redhawk668/ZX-Spectrum-S-Video/IMG_20200522_165719.jpg

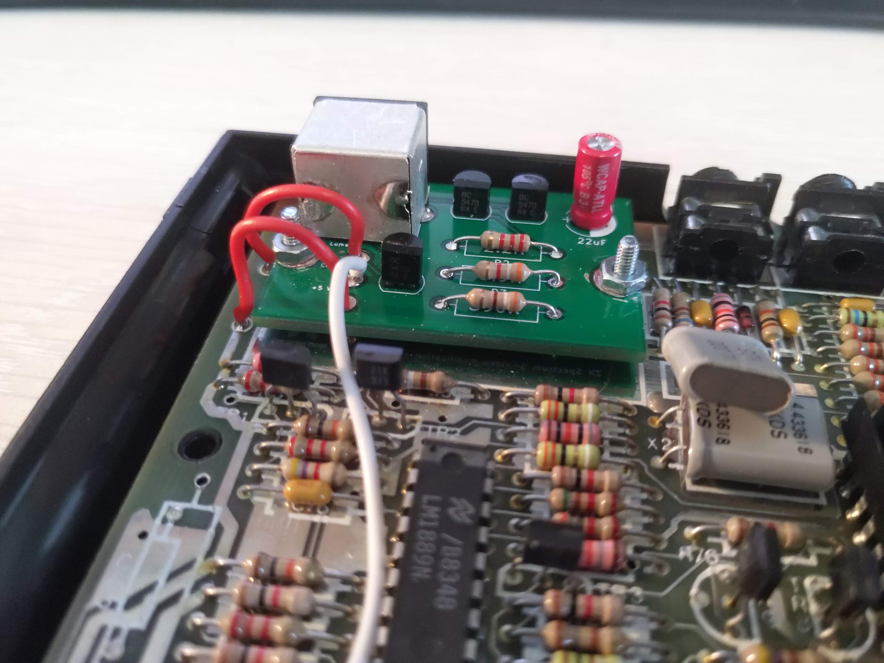
IMG_20200522_165719.jpg
